gehennaXXIV/Pocket-SDVX-RP2040-Zero/pics/1.png

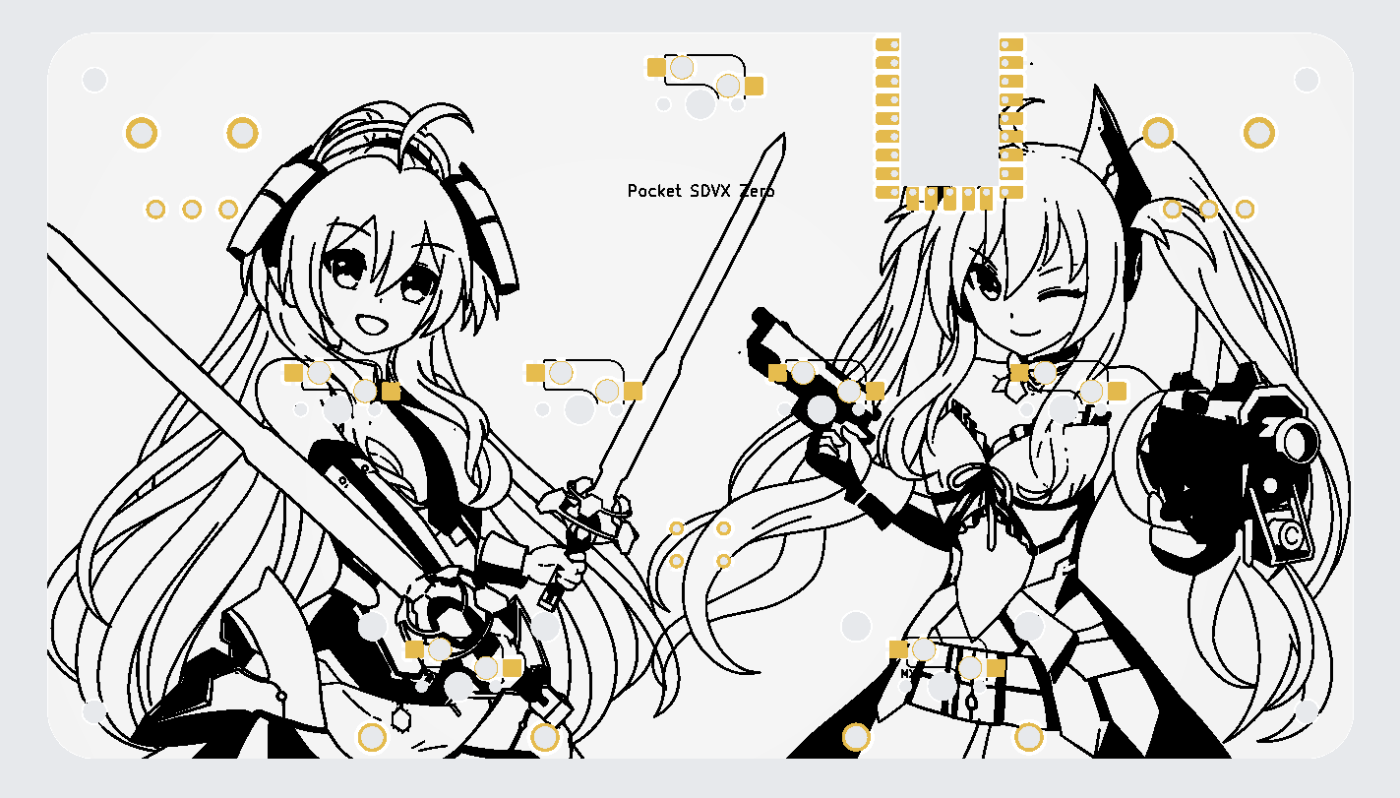
pics/1.png
