gehennaXXIV/Pocket-SDVX-RP2040-Zero/pics/2.png

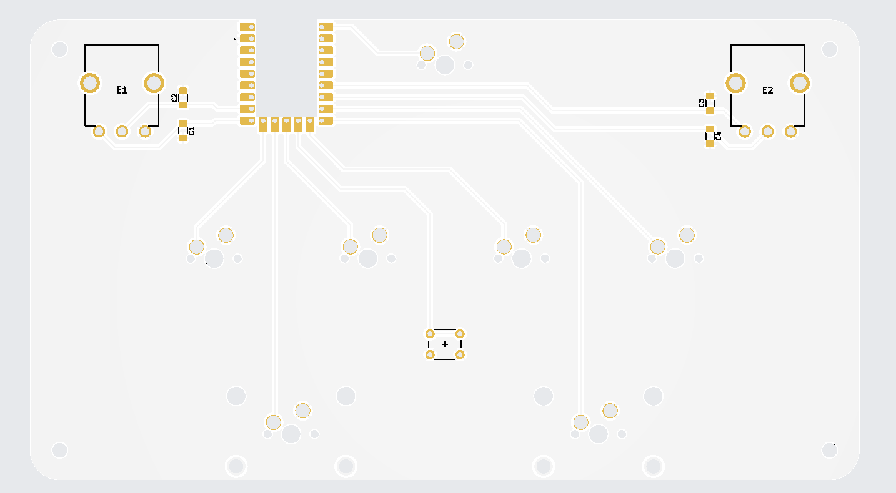
pics/2.png
